mairoleier/MRF89-AT-Module/Software/FW_MSP430FR5969_MRF89XA/HAL/include/timer.h

/*
 * timer.h
 *
 *  Created on: 24.11.2015
 *      Author: MAiro Leier
 */

#ifndef HAL_TIMER_H_
#define HAL_TIMER_H_

/***************************************************************************************************
 *	        Include section					                       		   					       *
 ***************************************************************************************************/
#include "system.h"

/***************************************************************************************************
 *	        Global Variable section  				                            				   *
 ***************************************************************************************************/



/***************************************************************************************************
 *	        Prototype section					                       							   *
 ***************************************************************************************************/
void TimerA0_Init(void);
void TimerA0_Start(void);
void TimerA0_Stop(void);
void TimerA0_Delay(uint16_t time_ms);


#endif /* HAL_TIMER_H_ */
