mairoleier/MRF89-AT-Module/Software/FW_MSP430FR5969_MRF89XA/Radio/NWK/nwk_security.c

/***************************************************************************************************
 *	        Include section					                       		   					       *
 ***************************************************************************************************/
#include "../../HAL/include/system.h"
#include "aes.h"
#include "../LNK/radio.h"

/***************************************************************************************************
 *	        Define section					                       		   					       *
 ***************************************************************************************************/


/***************************************************************************************************
 *	        Prototype section					                       							   *
 ***************************************************************************************************/


/***************************************************************************************************
 *	        Global Variable section  				                            				   *
 ***************************************************************************************************/
uint8_t encryption_key[] = {0x00, 0x01, 0x02, 0x03, 0x04, 0x05, 0x06, 0x07,
                          0x08, 0x09, 0x0a, 0x0b, 0x0c, 0x0d, 0x0e, 0x0f};


// *************************************************************************************************
// @fn          Payload_Encrypt
// @brief       Encrypt payload with 128-bit AES
// @param       uint8 msg[]				Message to be encrypted
// @return		uint8 EXIT_NO_ERROR
// *************************************************************************************************
uint8_t Payload_Encrypt(uint8_t *msg) {
	aes_encrypt(msg, encryption_key);
	return EXIT_NO_ERROR;
}


// *************************************************************************************************
// @fn          Payload_Decrypt
// @brief       Decrypt payload with 128-bit AES
// @param       uint8 msg[]				Message to be encrypted
// @return		uint8 EXIT_NO_ERROR
// *************************************************************************************************
uint8_t Payload_Decrypt(uint8_t *msg) {
	aes_decrypt(msg, encryption_key);
	return EXIT_NO_ERROR;
}
