mairoleier/MRF89-AT-Module/Software/FW_MSP430FR5969_MRF89XA/Radio/drivers/rf_time.c

/*
 * rf_time.c
 *
 *  Created on: 24.11.2015
 *      Author: MAiro Leier
 */
/***************************************************************************************************
 *	        Include section					                       		   					       *
 ***************************************************************************************************/
#include "rf_time.h"

/***************************************************************************************************
 *	        Define section					                       		   					       *
 ***************************************************************************************************/


/***************************************************************************************************
 *	        Prototype section					                       							   *
 ***************************************************************************************************/


/***************************************************************************************************
 *	        Global Variable section  				                            				   *
 ***************************************************************************************************/

// *************************************************************************************************
// @fn          RF_SPI_Init
// @brief       Enable RF Chip Select pins + Initialize SPI system
// @param       none
// @return      none
// *************************************************************************************************
void RF_Delay_In_Ms(uint16_t delay_ms) {
	//uint32_t timeout = SYSTEM_SPEED_MHZ*10*timeout_ms;		// Timeout in ms
}
