mairoleier/MRF89-AT-Module/Software/FW_MSP430FR5969_MRF89XA/Radio/drivers/rf_time.h

/*
 * rf_delay.h
 *
 *  Created on: 24.11.2015
 *      Author: MAiro Leier
 */

#ifndef RADIO_DRIVERS_RF_TIME_H_
#define RADIO_DRIVERS_RF_TIME_H_

/***************************************************************************************************
 *	        Include section					                       		   					       *
 ***************************************************************************************************/
#include <stdint.h>

/***************************************************************************************************
 *	        Define section					                       		   					       *
 ***************************************************************************************************/


/***************************************************************************************************
 *	        Prototype section					                       							   *
 ***************************************************************************************************/
void RF_Delay_In_Ms(uint16_t delay_ms);


/***************************************************************************************************
 *	        Global Variable section  				                            				   *
 ***************************************************************************************************/


#endif /* RADIO_DRIVERS_RF_TIME_H_ */
